ambariz/S3-MK1/assets/readme-assets/combine.png

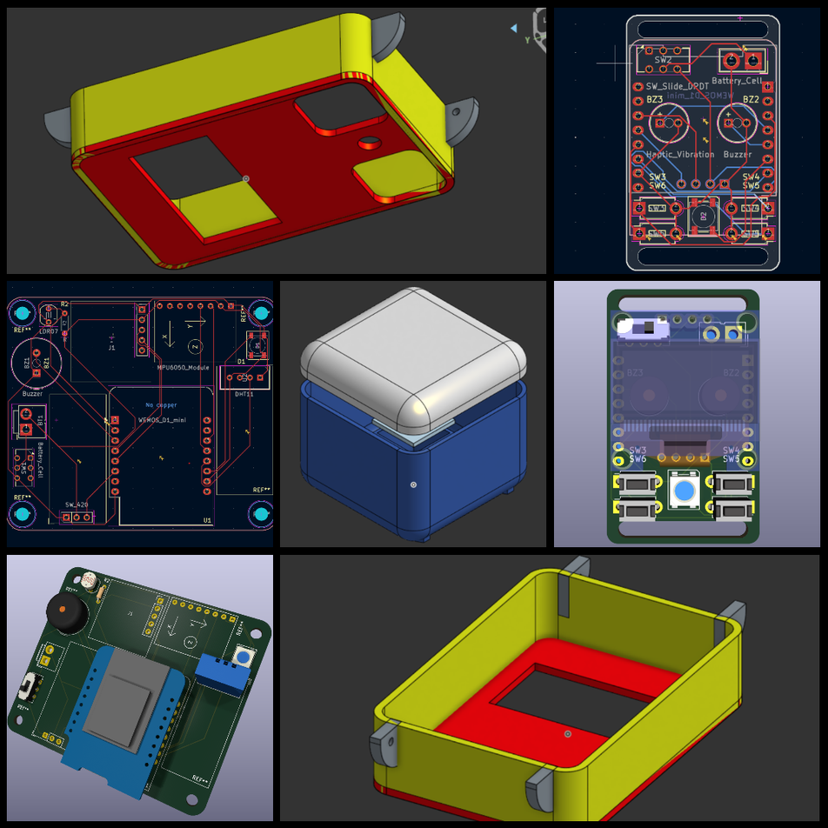
assets/readme-assets/combine.png
