ambariz/S3-MK1/firmware/s3_watch/shield_64_64_28f.h

#ifndef SHIELD_64_64_28F_H
#define SHIELD_64_64_28F_H

// Animation: shield 64×64 28f
// Size: 64x64, Frames: 36

#include <Arduino.h>

static const unsigned char shield_64_64_28f_frames[36][512] PROGMEM = {
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
};

static int shield_64_64_28f_frame = 0;

#endif // SHIELD_64_64_28F_H
