ambariz/S3-MK1/firmware/s3_watch/palm_scan_64_64_28f.h

#ifndef PALM_SCAN_64_64_28F_H
#define PALM_SCAN_64_64_28F_H

// Animation: palm-scan 64×64 28f
// Size: 64x64, Frames: 28

#include <Arduino.h>

static const unsigned char palm_scan_64_64_28f_frames[28][512] PROGMEM = {
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
};

static int palm_scan_64_64_28f_frame = 0;

#endif // PALM_SCAN_64_64_28F_H
